sokrasins/cgm-lamp/code/src/lamp.rs

pub mod lamp {
    use crate::server::server::{ServableData, ServableDataReq, ServableDataRsp, ServerData};
    use crate::storage::storage::Storable;
    use crate::sys::sys::uptime;
    use esp_idf_hal::{gpio::OutputPin, peripheral::Peripheral, rmt::RmtChannel};
    use log::info;
    use rgb_led::{RGB8, WS2812RMT};
    use serde::{Deserialize, Serialize};
    use std::sync::mpsc;

    const SAVE_DELAY: u64 = 5;

    pub const COLOR_MAX: u8 = 255;

    pub const RED: RGB8 = RGB8 {
        r: COLOR_MAX,
        g: 0,
        b: 0,
    };
    pub const BLUE: RGB8 = RGB8 {
        r: 0,
        g: 0,
        b: COLOR_MAX,
    };
    pub const YELLOW: RGB8 = RGB8 {
        r: COLOR_MAX,
        g: COLOR_MAX,
        b: 0,
    };
    pub const BLACK: RGB8 = RGB8 { r: 0, g: 0, b: 0 };
    pub const WHITE: RGB8 = RGB8 {
        r: COLOR_MAX,
        g: COLOR_MAX,
        b: COLOR_MAX,
    };

    pub const GREEN: RGB8 = RGB8 {
        r: 0,
        g: COLOR_MAX,
        b: 0,
    };

    pub const PURPLE: RGB8 = RGB8 {
        r: COLOR_MAX,
        g: 0,
        b: COLOR_MAX,
    };

    #[allow(dead_code)]
    pub enum LedState {
        Steady(RGB8),
        Breathe(RGB8),
        Off,
    }

    impl LedState {
        pub fn from_glucose(value: isize) -> LedState {
            // Multi-colored colormap
            // Red -> Green -> Blue -> Purple
            match value {
                0..55 => LedState::Breathe(RED),
                55..152 => LedState::Steady(get_color_in_sweep(&RED, &GREEN, 152 - 55, value - 55)),
                152..250 => {
                    LedState::Steady(get_color_in_sweep(&GREEN, &BLUE, 250 - 152, value - 152))
                }
                250..300 => {
                    LedState::Steady(get_color_in_sweep(&BLUE, &PURPLE, 300 - 250, value - 250))
                }
                300..500 => LedState::Breathe(PURPLE),
                _ => LedState::Breathe(WHITE),
            }
        }
    }

    pub fn get_color_in_sweep(
        start_color: &RGB8,
        end_color: &RGB8,
        total: usize,
        idx: isize,
    ) -> RGB8 {
        let r_step = (end_color.r as f64 - start_color.r as f64) / (total as f64);
        let g_step = (end_color.g as f64 - start_color.g as f64) / (total as f64);
        let b_step = (end_color.b as f64 - start_color.b as f64) / (total as f64);

        RGB8::new(
            ((start_color.r as f64) + (idx as f64 * r_step)) as u8,
            ((start_color.g as f64) + (idx as f64 * g_step)) as u8,
            ((start_color.b as f64) + (idx as f64 * b_step)) as u8,
        )
    }

    pub struct Lamp<'a> {
        state: LedState,
        brightness: f32,
        on: bool,
        led: WS2812RMT<'a>,
        server_channel: Option<mpsc::Receiver<ServableDataReq>>,
        save_data: bool,
        last_changed: u64,
    }

    #[derive(Serialize, Deserialize)]
    struct NvsLampState {
        brightness: f32,
        on: bool,
    }

    pub fn set_bright(color: &RGB8, brightness: f32) -> RGB8 {
        RGB8 {
            r: ((color.r as f32) * brightness) as u8,
            g: ((color.g as f32) * brightness) as u8,
            b: ((color.b as f32) * brightness) as u8,
        }
    }

    impl<'a> Lamp<'a> {
        pub fn new(
            led: impl Peripheral<P = impl OutputPin> + 'static,
            channel: impl Peripheral<P = impl RmtChannel> + 'static,
        ) -> Self {
            let state = LedState::Off;
            let brightness = 0.25;
            let led = WS2812RMT::new(led, channel).unwrap();

            Lamp {
                state,
                brightness,
                led,
                on: true,
                server_channel: None,
                save_data: false,
                last_changed: 0,
            }
        }

        pub fn set_color(&mut self, color: LedState) {
            self.state = color;
            self.set_led();
        }

        pub fn set_brightness(&mut self, brightness: u8) {
            self.brightness = (brightness as f32) / 255.0;
            self.last_changed = uptime();
            self.save_data = true;
            self.set_led();
        }

        pub fn change_brightness(&mut self, brightness: i32) {
            // If the brightness is already max, don't change it

            self.brightness += (brightness as f32) / 255.0;

            // Don't let brightness be more than 1
            if self.brightness > 1.0 {
                self.brightness = 1.0;
            }

            // Don't let brightness be less than 0
            if self.brightness < 0.0 {
                self.brightness = 0.0;
            }

            self.last_changed = uptime();
            self.save_data = true;
            self.set_led();
        }

        pub fn on(&mut self) {
            self.on = true;
            self.last_changed = uptime();
            self.save_data = true;
            self.set_led();
        }

        pub fn off(&mut self) {
            self.on = false;
            self.last_changed = uptime();
            self.save_data = true;
            self.set_led();
        }

        pub fn toggle(&mut self) {
            self.on = !self.on;
            self.last_changed = uptime();
            self.save_data = true;
            self.set_led();
        }

        fn set_led(&mut self) {
            match self.state {
                LedState::Steady(color) => self
                    .led
                    .set_pixel(set_bright(
                        &color,
                        self.brightness * (self.on as i32 as f32),
                    ))
                    .unwrap(),
                LedState::Breathe(color) => self
                    .led
                    .set_pixel(set_bright(
                        &color,
                        self.brightness * (self.on as i32 as f32),
                    ))
                    .unwrap(),
                LedState::Off => self.led.set_pixel(BLACK).unwrap(),
            };
        }

        fn get_nvs_state(&self) -> NvsLampState {
            NvsLampState {
                brightness: self.brightness,
                on: self.on,
            }
        }

        pub fn need_to_save(&self) -> bool {
            if self.save_data && (self.last_changed + SAVE_DELAY <= uptime()) {
                return true;
            }

            false
        }

        pub fn saved(&mut self) {
            self.save_data = false;
        }
    }

    impl<'a> Storable for Lamp<'a> {
        fn store_tag(&self) -> &str {
            return &"lamp_state";
        }

        fn store_data(&self) -> Vec<u8> {
            serde_json::to_string(&self.get_nvs_state())
                .unwrap()
                .into_bytes()
        }

        fn recall_data(&mut self, data: &[u8]) {
            let nvs_state = serde_json::from_slice::<NvsLampState>(data).unwrap();
            self.brightness = nvs_state.brightness;
            self.on = nvs_state.on;
        }
    }

    impl<'a> ServableData for Lamp<'a> {
        fn get_channel(&mut self) -> mpsc::Sender<ServableDataReq> {
            let (tx, rx) = mpsc::channel::<ServableDataReq>();
            self.server_channel = Some(rx);
            tx
        }

        fn handle_server_req(&mut self) {
            if let Some(channel) = &self.server_channel {
                if let Ok(req) = channel.try_recv() {
                    info!("lamp got a request from server");

                    if let ServableDataReq::Get(back_channel) = &req {
                        info!("Sending lamp state to server");
                        let mut rsp = ServerData::new();
                        rsp.brightness = Some((self.brightness * 255.0) as i32 as u8);
                        rsp.on = Some(self.on);
                        back_channel.send(ServableDataRsp::Data(rsp)).unwrap();
                    }

                    if let ServableDataReq::Set(update) = &req {
                        // If we got a brightness, then change our value
                        if let Some(brightness) = &update.brightness {
                            self.set_brightness(*brightness);
                        }

                        // If we got a power state, then change our value
                        if let Some(on) = &update.on {
                            if *on {
                                self.on();
                                self.last_changed = uptime();
                                self.save_data = true;
                            } else {
                                self.off();
                                self.last_changed = uptime();
                                self.save_data = true;
                            }
                        }
                    }

                    if let ServableDataReq::Reset = &req {
                        self.on();
                        self.brightness = 0.25f32;
                        self.last_changed = uptime();
                        self.save_data = true;
                    }
                }
            }
        }
    }
}
